szbeni/forcegauge/fw/forcegauge-esp32/httpServer.ino

// UDP broadcast
WiFiUDP udpBroadcaster;

#include <lwip/sockets.h>
#include <lwip/netdb.h>
#include <errno.h>

int broadcastAddress(void)
{
  // static int udp_server = -1;
  // static struct sockaddr_in recipient;
  // static struct in_addr localInterface;

  // if (udp_server == -1)
  // {
  //   if ((udp_server = socket(AF_INET, SOCK_DGRAM, 0)) == -1)
  //   {
  //     log_e("could not create socket: %d", errno);
  //     return 0;
  //   }
  //   fcntl(udp_server, F_SETFL, O_NONBLOCK);
  //   struct in_addr iaddr = {0};

  //   IPAddress remote_ip;
  //   remote_ip.fromString("255.255.255.255");
  //   int remote_port = 65123;
  //   recipient.sin_addr.s_addr = (uint32_t)remote_ip;
  //   recipient.sin_family = AF_INET;
  //   recipient.sin_port = htons(remote_port);
  // }
  // localInterface.s_addr = inet_addr("192.168.4.1");
  // int err = setsockopt(udp_server, IPPROTO_IP, IP_MULTICAST_IF, &localInterface, sizeof(localInterface));
  // if (err < 0)
  // {
  //   log_e(V4TAG, "Failed to set IP_MULTICAST_IF. Error %d", errno);
  //   return 0;
  // }

  // int sent = sendto(udp_server, "forcegauge", 10, 0, (struct sockaddr *)&recipient, sizeof(recipient));
  // if (sent < 0)
  // {
  //   log_e("could not send data: %d", errno);
  //   return 0;
  // }
  // return 1;

  // // const uint8_t *msg = (const uint8_t *)(getAboutString().c_str());
  // // size_t len = strlen((const char *)msg);
  udpBroadcaster.beginPacket("255.255.255.255", 65123);
  udpBroadcaster.write((uint8_t *)"forcegauge", 10);
  udpBroadcaster.endPacket();
  return 1;
}

#define FILESYSTEM SPIFFS
#define DBG_OUTPUT_PORT Serial

WebServer server(80);

File fsUploadFile;
DNSServer dnsServer;
IPAddress apIP(192, 168, 4, 1);
const byte DNS_PORT = 53;

bool exists(String path)
{
  bool yes = false;
  File file = FILESYSTEM.open(path, "r");
  if (!file.isDirectory())
  {
    yes = true;
  }
  file.close();
  return yes;
}

bool handleFileRead(String path)
{
  DBG_OUTPUT_PORT.println("handleFileRead: " + path);

  if (path.endsWith("/"))
  {
    path += "index.htm";
  }
  if (path.endsWith(configFilename))
    saveConfig(&config);

  String contentType = getContentType(path);
  String pathWithGz = path + ".gz";
  if (exists(pathWithGz) || exists(path))
  {
    if (exists(pathWithGz))
    {
      path += ".gz";
    }
    File file = FILESYSTEM.open(path, "r");
    server.streamFile(file, contentType);
    file.close();
    return true;
  }
  return false;
}

void handleFileUpload()
{
  if (server.uri() != "/edit")
  {
    return;
  }
  HTTPUpload &upload = server.upload();
  if (upload.status == UPLOAD_FILE_START)
  {
    String filename = upload.filename;
    if (!filename.startsWith("/"))
    {
      filename = "/" + filename;
    }
    DBG_OUTPUT_PORT.print("handleFileUpload Name: ");
    DBG_OUTPUT_PORT.println(filename);
    fsUploadFile = FILESYSTEM.open(filename, "w");
    filename = String();
  }
  else if (upload.status == UPLOAD_FILE_WRITE)
  {
    // DBG_OUTPUT_PORT.print("handleFileUpload Data: "); DBG_OUTPUT_PORT.println(upload.currentSize);
    if (fsUploadFile)
    {
      fsUploadFile.write(upload.buf, upload.currentSize);
    }
  }
  else if (upload.status == UPLOAD_FILE_END)
  {
    if (fsUploadFile)
    {
      fsUploadFile.close();
    }

    DBG_OUTPUT_PORT.print("handleFileUpload Size: ");
    DBG_OUTPUT_PORT.println(upload.totalSize);
    DBG_OUTPUT_PORT.println(upload.filename);
    if (String(upload.filename) == TABATA_FILE)
    {
      tabataHandler.refreshList();
    }
  }
}

void handleFileDelete()
{
  if (server.args() == 0)
  {
    return server.send(500, "text/plain", "BAD ARGS");
  }
  String path = server.arg(0);
  DBG_OUTPUT_PORT.println("handleFileDelete: " + path);
  if (path == "/")
  {
    return server.send(500, "text/plain", "BAD PATH");
  }
  if (!exists(path))
  {
    return server.send(404, "text/plain", "FileNotFound");
  }
  FILESYSTEM.remove(path);
  server.send(200, "text/plain", "");
  path = String();
}

void handleFileCreate()
{
  if (server.args() == 0)
  {
    return server.send(500, "text/plain", "BAD ARGS");
  }
  String path = server.arg(0);
  DBG_OUTPUT_PORT.println("handleFileCreate: " + path);
  if (path == "/")
  {
    return server.send(500, "text/plain", "BAD PATH");
  }
  if (exists(path))
  {
    return server.send(500, "text/plain", "FILE EXISTS");
  }
  File file = FILESYSTEM.open(path, "w");
  if (file)
  {
    file.close();
  }
  else
  {
    return server.send(500, "text/plain", "CREATE FAILED");
  }
  server.send(200, "text/plain", "");
  path = String();
}

void handleFileList()
{
  if (!server.hasArg("dir"))
  {
    server.send(500, "text/plain", "BAD ARGS");
    return;
  }

  String path = server.arg("dir");
  DBG_OUTPUT_PORT.println("handleFileList: " + path);

  File root = FILESYSTEM.open(path);
  path = String();

  String output = "[";
  if (root.isDirectory())
  {
    File file = root.openNextFile();
    while (file)
    {
      if (output != "[")
      {
        output += ',';
      }
      output += "{\"type\":\"";
      output += (file.isDirectory()) ? "dir" : "file";
      output += "\",\"name\":\"";
      output += String(file.path()).substring(1);
      output += "\"}";
      file = root.openNextFile();
    }
  }
  output += "]";
  server.send(200, "text/json", output);
}

String getContentType(String filename)
{
  if (server.hasArg("download"))
  {
    return "application/octet-stream";
  }
  else if (filename.endsWith(".htm"))
  {
    return "text/html";
  }
  else if (filename.endsWith(".html"))
  {
    return "text/html";
  }
  else if (filename.endsWith(".css"))
  {
    return "text/css";
  }
  else if (filename.endsWith(".js"))
  {
    return "application/javascript";
  }
  else if (filename.endsWith(".png"))
  {
    return "image/png";
  }
  else if (filename.endsWith(".gif"))
  {
    return "image/gif";
  }
  else if (filename.endsWith(".jpg"))
  {
    return "image/jpeg";
  }
  else if (filename.endsWith(".ico"))
  {
    return "image/x-icon";
  }
  else if (filename.endsWith(".xml"))
  {
    return "text/xml";
  }
  else if (filename.endsWith(".pdf"))
  {
    return "application/x-pdf";
  }
  else if (filename.endsWith(".zip"))
  {
    return "application/x-zip";
  }
  else if (filename.endsWith(".gz"))
  {
    return "application/x-gzip";
  }
  return "text/plain";
}

void handleConfigUpdate()
{
  bool wasConfig = false;
  for (int i = 0; i < server.args(); i++)
  {
    if (configJSON.containsKey(server.argName(i)))
    {
      configJSON[server.argName(i)] = server.arg(i);
      wasConfig = true;
    }
  }
  if (wasConfig)
  {
    copyConfig(&config);
    saveConfig(&config);
    handleFileRead("/index.htm");
  }
  else
  {
    handleFileRead("/configure.htm");
  }
}

bool loggedIn = false;
void handleLoginPage()
{
  Serial.println("Login page");
  Serial.println(loggedIn);
  if (loggedIn == false)
  {
    // if (server.method() == HTTP_POST)
    //{
    server.send(204, "text/plain", "Logged in");
    // handleConfigUpdate();
    loggedIn = true;
    //}
    // else
    //{
    // Serve configure
    //  handleFileRead("./login.htm");
    //}
  }
  else
  {
    server.send(204);
  }
}

String getAboutString(void)
{
  String response = "type:forcegauge\n";
  response += "name:" + String(config.name) + "\n";
  response += "version:" + String(version) + "\n";
  return response;
}

void handleAbout()
{
  server.send(200, "text/plane", getAboutString());
}

// void webSocketBroadcastData()
//{
//   if (ws.count())
//   {
//     String jsonObj = "{\"data\": [";
//     jsonObj += "{\"time\":\"" + String(data->t) + "\", ";
//     jsonObj += "\"raw\":\"" + String(data->v) + "\", ";
//     jsonObj += "\"value\":\"" + String(config.lastValue) + "\"}";
//     jsonObj += "]}";
//     ws.textAll(jsonObj);
//   }
// }

const char *firmwareUpdateHtml = "<form method='POST' action='/update' enctype='multipart/form-data'><input type='file' name='update'><input type='submit' value='Update'></form>";
void handleUpdateFinish()
{
  server.sendHeader("Connection", "close");
  server.send(200, "text/plain", (Update.hasError()) ? "FAIL" : "OK");
  ESP.restart();
}

void handleUpdateStart()
{
  HTTPUpload &upload = server.upload();
  if (upload.status == UPLOAD_FILE_START)
  {
    Serial.setDebugOutput(true);
    Serial.printf("Update: %s\n", upload.filename.c_str());
    if (!Update.begin())
    { // start with max available size
      Update.printError(Serial);
    }
  }
  else if (upload.status == UPLOAD_FILE_WRITE)
  {
    if (Update.write(upload.buf, upload.currentSize) != upload.currentSize)
    {
      Update.printError(Serial);
    }
  }
  else if (upload.status == UPLOAD_FILE_END)
  {
    if (Update.end(true))
    { // true to set the size to the current progress
      Serial.printf("Update Success: %u\nRebooting...\n", upload.totalSize);
    }
    else
    {
      Update.printError(Serial);
    }
    Serial.setDebugOutput(false);
  }
  else
  {
    Serial.printf("Update Failed Unexpectedly (likely broken connection): status=%d\n", upload.status);
  }
}

// check if this string is an IP address
boolean isIp(String str)
{
  for (size_t i = 0; i < str.length(); i++)
  {
    int c = str.charAt(i);
    if (c != '.' && (c < '0' || c > '9'))
    {
      return false;
    }
  }
  return true;
}

String toStringIp(IPAddress ip)
{
  String res = "";
  for (int i = 0; i < 3; i++)
  {
    res += String((ip >> (8 * i)) & 0xFF) + ".";
  }
  res += String(((ip >> 8 * 3)) & 0xFF);
  return res;
}

boolean captivePortal()
{
  Serial.println("Captive portal:");
  Serial.println(server.hostHeader());
  if (!isIp(server.hostHeader()))
  {
    Serial.println("Request redirected to captive portal");
    server.sendHeader("Location", String("http://") + toStringIp(server.client().localIP()), true);
    server.send(302, "text/plain", "");
    server.client().stop();
    return true;
  }
  return false;
}

void handleRoot()
{
  if (captivePortal())
  {
    return;
  }
  server.sendHeader("Cache-Control", "no-cache, no-store, must-revalidate");
  server.sendHeader("Pragma", "no-cache");
  server.sendHeader("Expires", "-1");

  String p;
  p += F(
      "<html><head></head><body>"
      "<h1>Connected!</h1>");
  p += F("</body></html>");

  server.send(200, "text/html", p);
}

void httpServerTask(void *parameter)
{
  Serial.print("httpServerTask: priority = ");
  Serial.println(uxTaskPriorityGet(NULL));

  dnsServer.start(DNS_PORT, "*", apIP);

  MDNS.addService("http", "tcp", 80);
  MDNS.begin(config.name);
  DBG_OUTPUT_PORT.print("Open http://");
  DBG_OUTPUT_PORT.print(config.name);
  DBG_OUTPUT_PORT.println(".local/");

  // SERVER INIT
  server.on("/list", HTTP_GET, handleFileList);
  server.on("/edit", HTTP_GET, []()
            {
    if (!handleFileRead("/edit.htm")) {
      server.send(404, "text/plain", "FileNotFound");
    } });
  server.on("/edit", HTTP_PUT, handleFileCreate);
  server.on("/edit", HTTP_DELETE, handleFileDelete);
  server.on(
      "/edit", HTTP_POST, []()
      { server.send(200, "text/plain", ""); },
      handleFileUpload);

  // server.on("/", handleRoot);
  server.on("/generate_204", handleRoot);
  server.on("/gen_204", handleRoot);
  server.on("/configure.htm", HTTP_POST, handleConfigUpdate);
  server.on("/about", handleAbout);
  server.on("/login", handleLoginPage);

  server.on("/updatewebota", handleUpdateWebOTA);
  server.on("/update", HTTP_GET, []()
            {
      server.sendHeader("Connection", "close");
      server.send(200, "text/html", firmwareUpdateHtml); });
  server.on("/update", HTTP_POST, handleUpdateFinish, handleUpdateStart);
  server.onNotFound([]()
                    {
    if (!handleFileRead(server.uri())) {
      if (captivePortal()) { 
        return;
      }
      server.send(404, "text/plain", "FileNotFound");
    } });

  // get heap status, analog input value and all GPIO statuses in one json call
  server.on("/all", HTTP_GET, []()
            {
    String json = "{";
    json += "\"heap\":" + String(ESP.getFreeHeap());
    json += ", \"analog\":" + String(analogRead(A1));
    json += ", \"gpio\":" + String((uint32_t)(0));
    json += "}";
    server.send(200, "text/json", json);
    json = String(); });
  server.begin();
  DBG_OUTPUT_PORT.println("HTTP server started");

  unsigned long previous_time = 0;
  while (1)
  {
    if (millis() - previous_time > 2000)
    {
      previous_time = millis();
      broadcastAddress();
    }

    // checkWifiConnection(config.ssid1, config.passwd1);
    dnsServer.processNextRequest();
    server.handleClient();

    delay(10);
  }

  // Should never get here
  vTaskDelete(NULL);
}
