szbeni/forcegauge/fw/forcegauge-esp32/hx711_custom.cpp

#include <Arduino.h>
#include "hx711_custom.h"

HX711::HX711(byte dout, byte pd_sck, byte gain)
{
	begin(dout, pd_sck, gain);
}

HX711::HX711()
{
}

HX711::~HX711()
{
}

void HX711::begin(byte dout, byte pd_sck, byte gain)
{
	PD_SCK = pd_sck;
	DOUT = dout;

	pinMode(PD_SCK, OUTPUT);
	pinMode(DOUT, INPUT);

	set_gain(gain);
}

bool HX711::is_ready()
{
	return digitalRead(DOUT) == LOW;
}

void HX711::set_gain(byte gain)
{
	Serial.print("Gain: ");
	Serial.println(gain);

	switch (gain)
	{
	case 128: // channel A, gain factor 128
		GAIN = 1;
		break;
	case 64: // channel A, gain factor 64
		GAIN = 3;
		break;
	case 32: // channel B, gain factor 32
		GAIN = 2;
		break;
	}

	digitalWrite(PD_SCK, LOW);
	read();
}

long HX711::read()
{
	unsigned long startedWaiting = millis();
	// wait for the chip to become ready or timeout in 100ms
	while (!is_ready())
	{
		if (millis() - startedWaiting >= 100)
		{
			return 0;
		}
	}

	unsigned long value = 0;
	uint8_t data[3] = {0};
	uint8_t filler = 0x00;

	// pulse the clock pin 24 times to read the data
	data[2] = shiftInSlow(DOUT, PD_SCK, MSBFIRST);
	data[1] = shiftInSlow(DOUT, PD_SCK, MSBFIRST);
	data[0] = shiftInSlow(DOUT, PD_SCK, MSBFIRST);

	// set the channel and the gain factor for the next reading using the clock pin
	for (unsigned int i = 0; i < GAIN; i++)
	{
		digitalWrite(PD_SCK, HIGH);
		delayMicroseconds(2);
		digitalWrite(PD_SCK, LOW);
		delayMicroseconds(2);
	}

	// Replicate the most significant bit to pad out a 32-bit signed integer
	if (data[2] & 0x80)
	{
		filler = 0xFF;
	}
	else
	{
		filler = 0x00;
	}

	// Construct a 32-bit signed integer
	value = (static_cast<unsigned long>(filler) << 24 | static_cast<unsigned long>(data[2]) << 16 | static_cast<unsigned long>(data[1]) << 8 | static_cast<unsigned long>(data[0]));

	return static_cast<long>(value);
}

long HX711::read_average(byte times)
{
	long sum = 0;
	for (byte i = 0; i < times; i++)
	{
		sum += read();
	}
	return sum / times;
}

double HX711::get_value(byte times)
{
	return read_average(times) - OFFSET;
}

float HX711::get_units(byte times)
{
	return get_value(times) / SCALE;
}

void HX711::tare(byte times)
{
	double sum = read_average(times);
	set_offset(sum);
}

void HX711::set_scale(float scale)
{
	SCALE = scale;
}

float HX711::get_scale()
{
	return SCALE;
}

void HX711::set_offset(long offset)
{
	OFFSET = offset;
}

long HX711::get_offset()
{
	return OFFSET;
}

void HX711::power_down()
{
	digitalWrite(PD_SCK, LOW);
	digitalWrite(PD_SCK, HIGH);
}

void HX711::power_up()
{
	digitalWrite(PD_SCK, LOW);
}

uint8_t HX711::shiftInSlow(uint8_t dataPin, uint8_t clockPin, uint8_t bitOrder)
{
	uint8_t value = 0;
	uint8_t i;

	for (i = 0; i < 8; ++i)
	{
		digitalWrite(clockPin, HIGH);
		delayMicroseconds(2);
		if (bitOrder == LSBFIRST)
			value |= digitalRead(dataPin) << i;
		else
			value |= digitalRead(dataPin) << (7 - i);
		digitalWrite(clockPin, LOW);
		delayMicroseconds(2);
	}
	return value;
}
